M0RCHED/skadi_6_bay/hardware/6_bay_charg/6_bay_charg.kicad_sch

## KiCad design hardware/6_bay_charg/6_bay_charg.kicad_sch (2026-03-02, an earlier design)

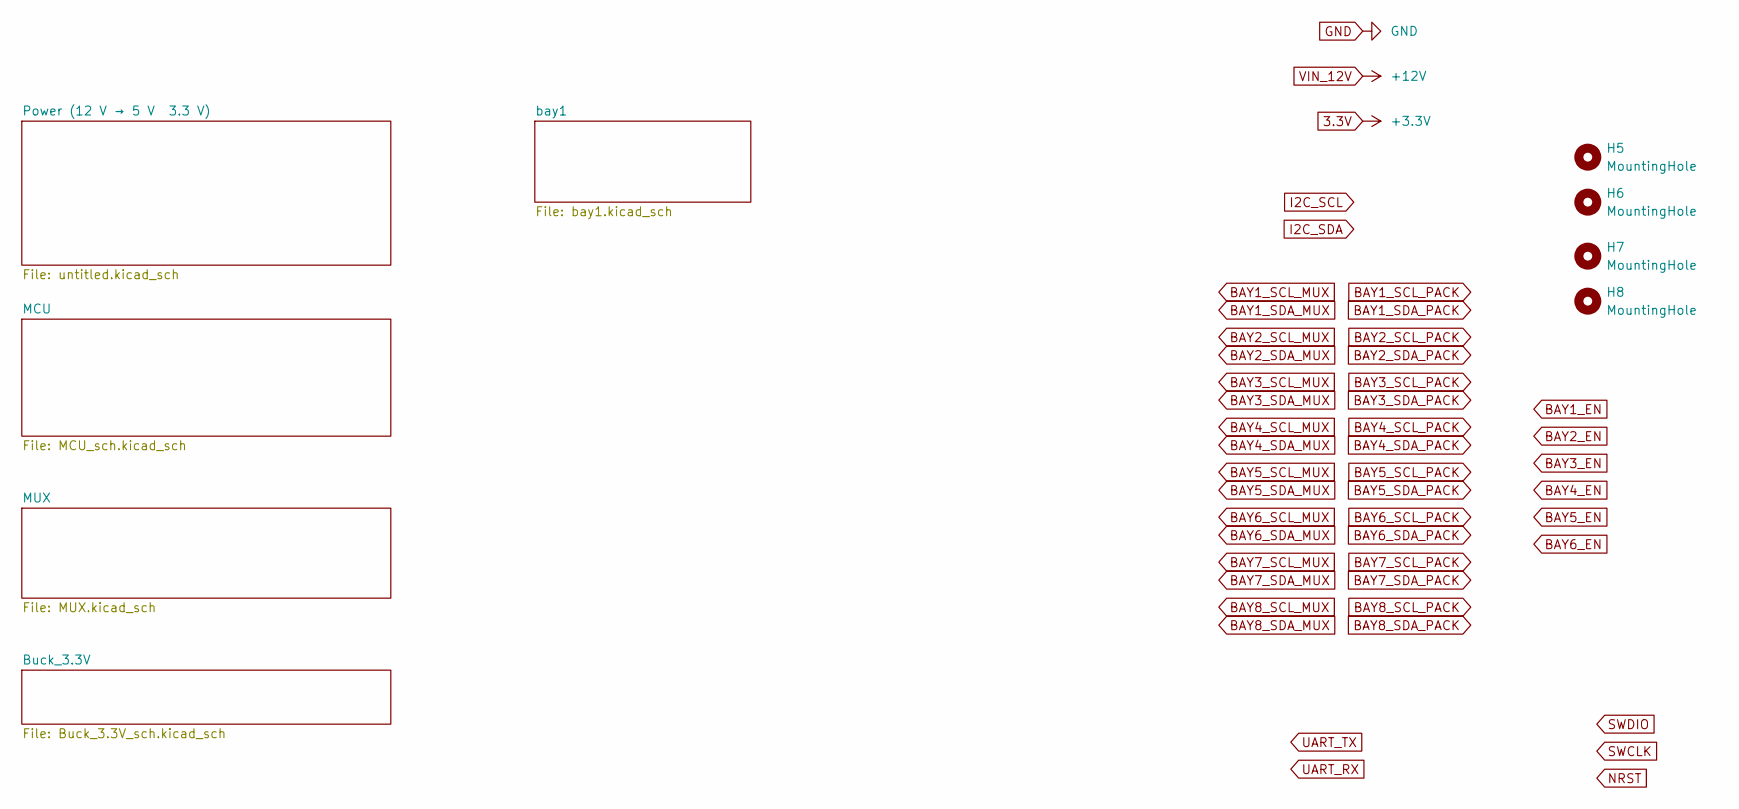
[picture p15: schematic 6_bay_charg.kicad_sch]

Parts:
H5, H6, H7, H8: MountingHole; MountingHole_2.2mm_M2
