M0RCHED/skadi_6_bay/hardware/6_bay_charg/Buck_3.3V_sch.kicad_sch

## KiCad design hardware/6_bay_charg/Buck_3.3V_sch.kicad_sch (2026-03-03, an earlier design)

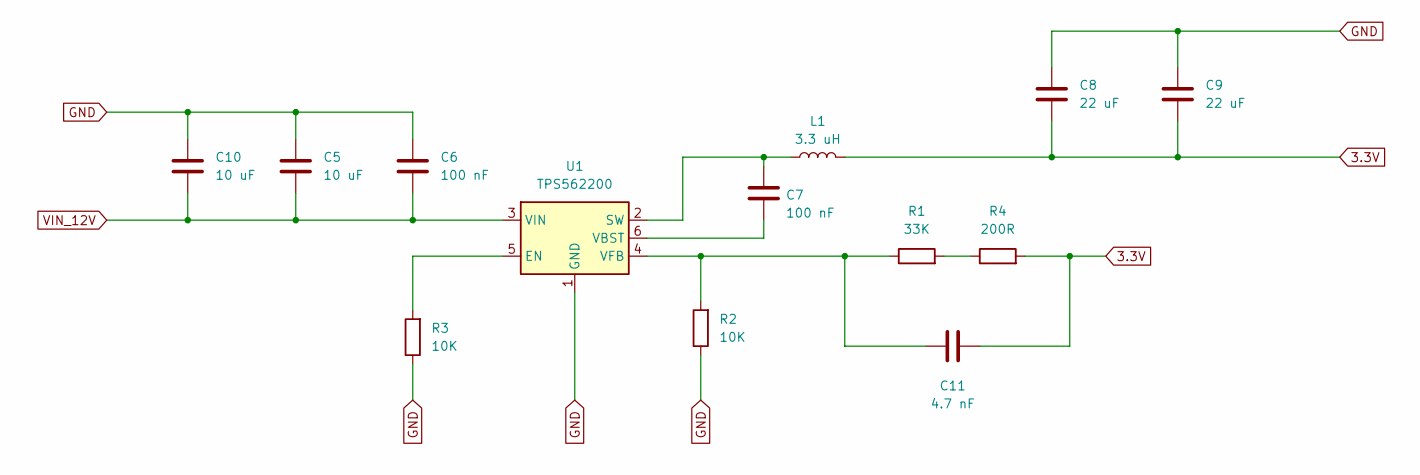
[picture p16: schematic Buck_3.3V_sch.kicad_sch]

Parts:
C5, C10: 10 uF
C6, C7: 100 nF
C8, C9: 22 uF
C11: 4.7 nF
L1: 3.3 uH
R1: 33K
R2, R3: 10K
R4: 200R
U1: TPS562200; SOT-23-6

Connections:
3.3V: C8.2, C9.2, C11.2, L1.2, R4.2
GND: C5.2, C6.1, C8.1, C9.1, C10.2, R2.1, R3.1, U1.1 (GND)
unnamed: C7.1, U1.6 (VBST)
unnamed: C7.2, L1.1, U1.2 (SW)
unnamed: C11.1, R1.1, R2.2, U1.4 (VFB)
unnamed: R1.2, R4.1
unnamed: R3.2, U1.5 (EN)
VIN_12V: C5.1, C6.2, C10.1, U1.3 (VIN)
