M0RCHED/skadi_6_bay/hardware/6_bay_charg/LEDs_driver.kicad_sch

## KiCad design hardware/6_bay_charg/LEDs_driver.kicad_sch (2026-01-14, an earlier design)

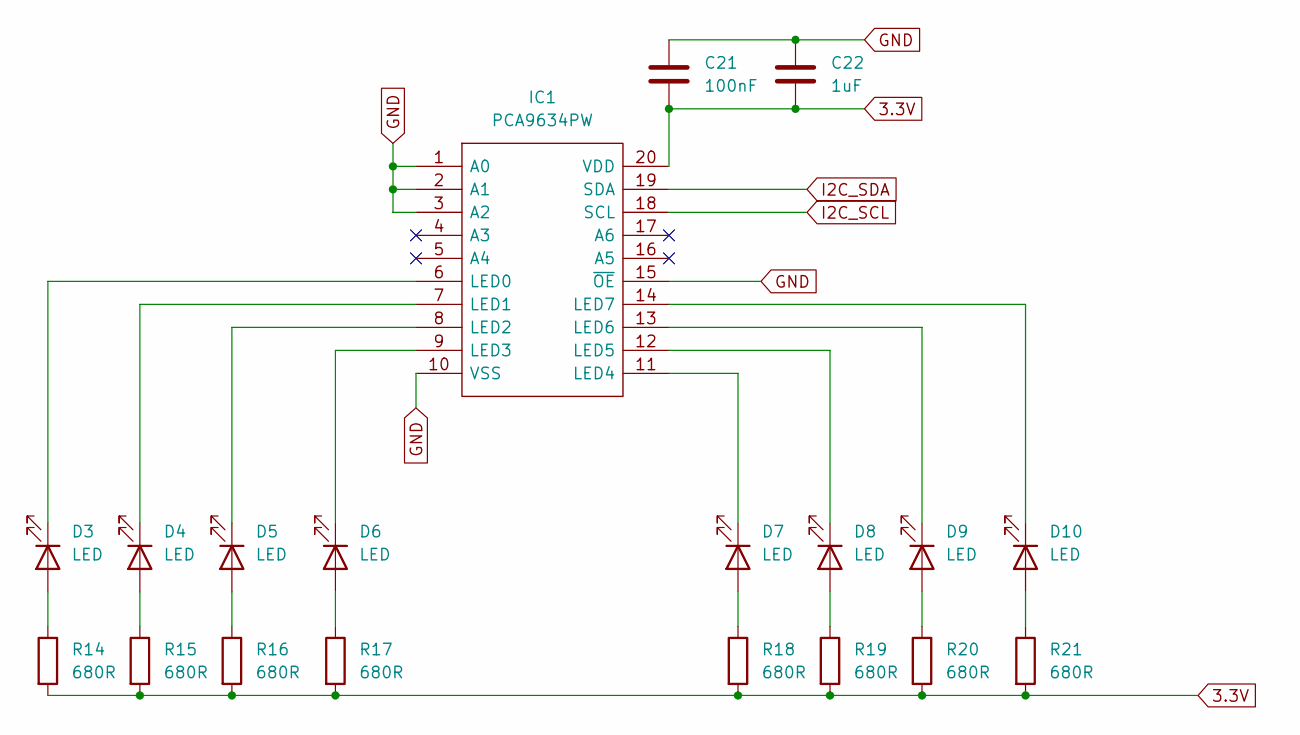
[picture p17: schematic LEDs_driver.kicad_sch]

Parts:
C21: 100nF
C22: 1uF
D3, D4, D5, D6, D7, D8, D9, D10: LED
IC1: PCA9634PW; SOP65P640X110-20N; Manufacturer_Part_Number PCA9634PW; Mouser Part Number 771-PCA9634PW
R14, R15, R16, R17, R18, R19, R20, R21: 680R

Connections:
3.3V: C21.2, C22.2, IC1.20 (VDD), R14.2, R15.2, R16.2, R17.2, R18.2, R19.2, R20.2, R21.2
GND: C21.1, C22.1, IC1.1 (A0), IC1.2 (A1), IC1.3 (A2), IC1.10 (VSS), IC1.15 (~OE)
I2C_SCL: IC1.18 (SCL)
I2C_SDA: IC1.19 (SDA)
unnamed: D3.1 (K), IC1.6 (LED0)
unnamed: D3.2 (A), R14.1
unnamed: D4.1 (K), IC1.7 (LED1)
unnamed: D4.2 (A), R15.1
unnamed: D5.1 (K), IC1.8 (LED2)
unnamed: D5.2 (A), R16.1
unnamed: D6.1 (K), IC1.9 (LED3)
unnamed: D6.2 (A), R17.1
unnamed: D7.1 (K), IC1.11 (LED4)
unnamed: D7.2 (A), R18.1
unnamed: D8.1 (K), IC1.12 (LED5)
unnamed: D8.2 (A), R19.1
unnamed: D9.1 (K), IC1.13 (LED6)
unnamed: D9.2 (A), R20.1
unnamed: D10.1 (K), IC1.14 (LED7)
unnamed: D10.2 (A), R21.1
