M0RCHED/skadi_6_bay/hardware/6_bay_charg/bay1.kicad_sch

## KiCad design hardware/6_bay_charg/bay1.kicad_sch (2026-03-02, an earlier design)

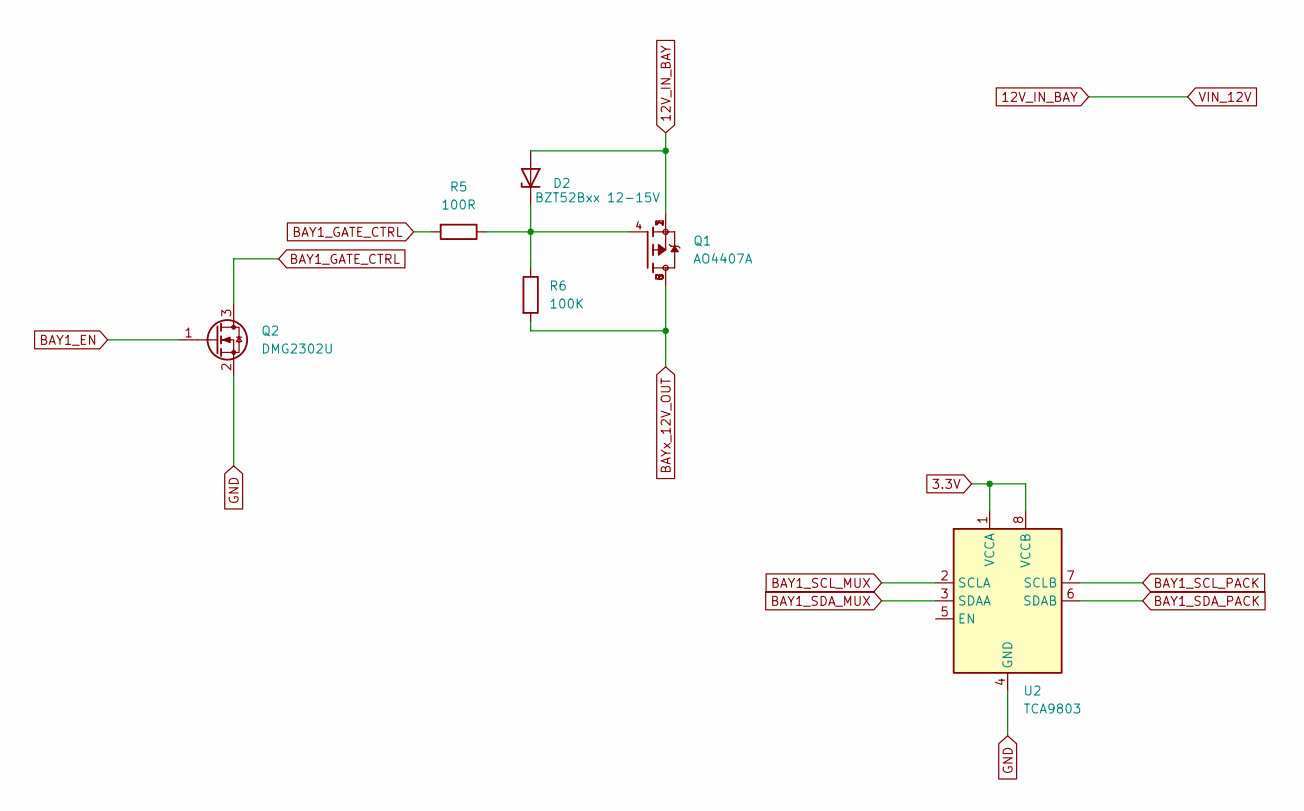
[picture p18: schematic bay1.kicad_sch]

Parts:
D2: BZT52Bxx 12-15V; D_SOD-123F
Q1: AO4407A; SOIC127P600X175-8N; PARTREV I
Q2: DMG2302U; SOT-23
R5: 100R
R6: 100K
U2: TCA9803; VSSOP-8_3x3mm_P0.65mm

Connections:
3.3V: U2.1 (VCCA), U2.8 (VCCB)
12V_IN_BAY: D2.2 (A), Q1.1, Q1.2, Q1.3
BAY1_EN: Q2.1 (G)
BAY1_GATE_CTRL: Q2.3 (D), R5.2
BAY1_SCL_MUX: U2.2 (SCLA)
BAY1_SCL_PACK: U2.7 (SCLB)
BAY1_SDA_MUX: U2.3 (SDAA)
BAY1_SDA_PACK: U2.6 (SDAB)
BAYx_12V_OUT: Q1.5, Q1.6, Q1.7, Q1.8, R6.2
GND: Q2.2 (S), U2.4 (GND)
unnamed: D2.1 (K), Q1.4, R5.1, R6.1
