M0RCHED/skadi_6_bay/hardware/6_bay_charg/power12v.kicad_sch

## KiCad design hardware/6_bay_charg/power12v.kicad_sch (2026-03-02)

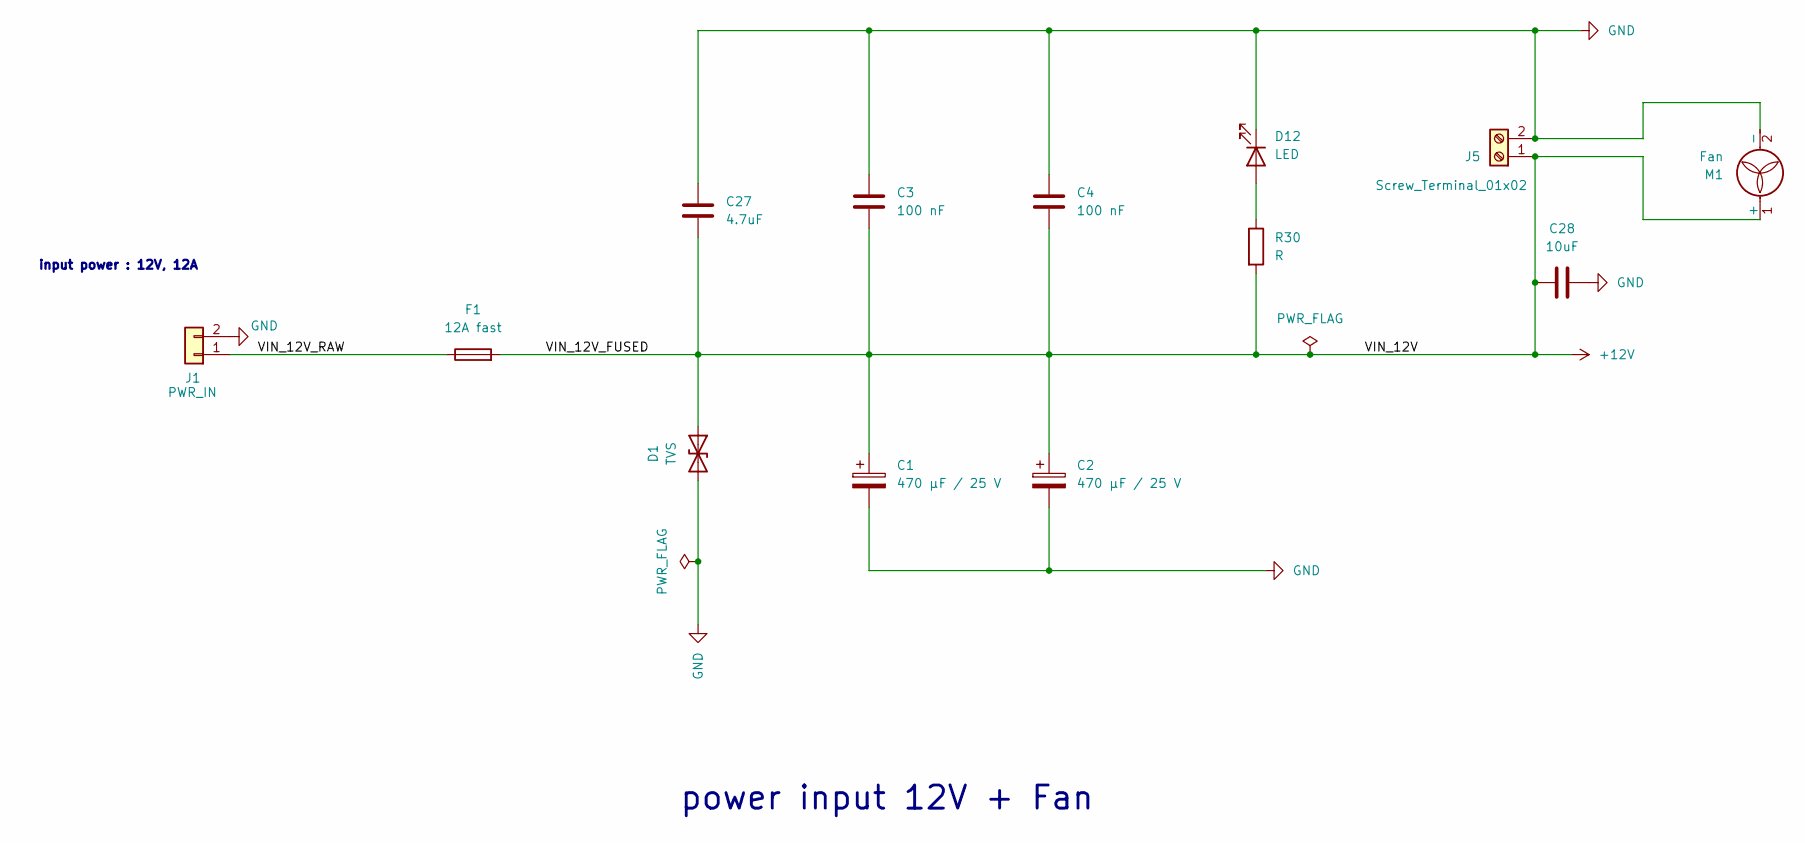
[picture p19: schematic power12v.kicad_sch]

Parts:
C1: 470 µF / 25 V; CP_Elec_8x10.5
C2: 470 µF / 25 V; C_1206_3216Metric
C3, C4: 100 nF
C27: 4.7uF
C28: 10uF
D1: TVS; D_SMA
D12: LED
F1: 12A fast
J1: PWR_IN; PhoenixContact_SPT_2.5_2-H-5.0_1x02_P5.0mm_Horizontal
J5: Screw_Terminal_01x02
M1: Fan
R30: R

Connections:
+12V: C1.1, C2.1, C3.2, C4.2, C27.2, C28.1, D1.1 (A1), F1.2, J5.1, M1.1 (+), R30.2
GND: C1.2, C2.2, C3.1, C4.1, C27.1, C28.2, D1.2 (A2), D12.1 (K), J1.2, J5.2, M1.2 (-)
unnamed: D12.2 (A), R30.1
VIN_12V_RAW: F1.1, J1.1

Notes on the sheet:
power input 12V + Fan
input power : 12V, 12A
